geekmengran/MQ/2.Images/MQ-F-v1p5.png

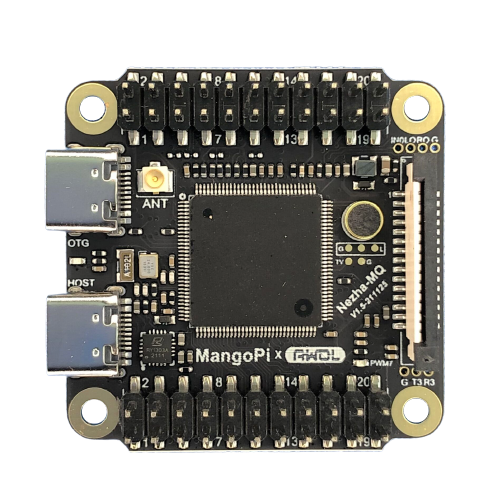
2.Images/MQ-F-v1p5.png
