geekmengran/MQ/3.Docs/MQ_SCH_v1.5.pdf

# J3USB-TypeC-16P

5.1K R80

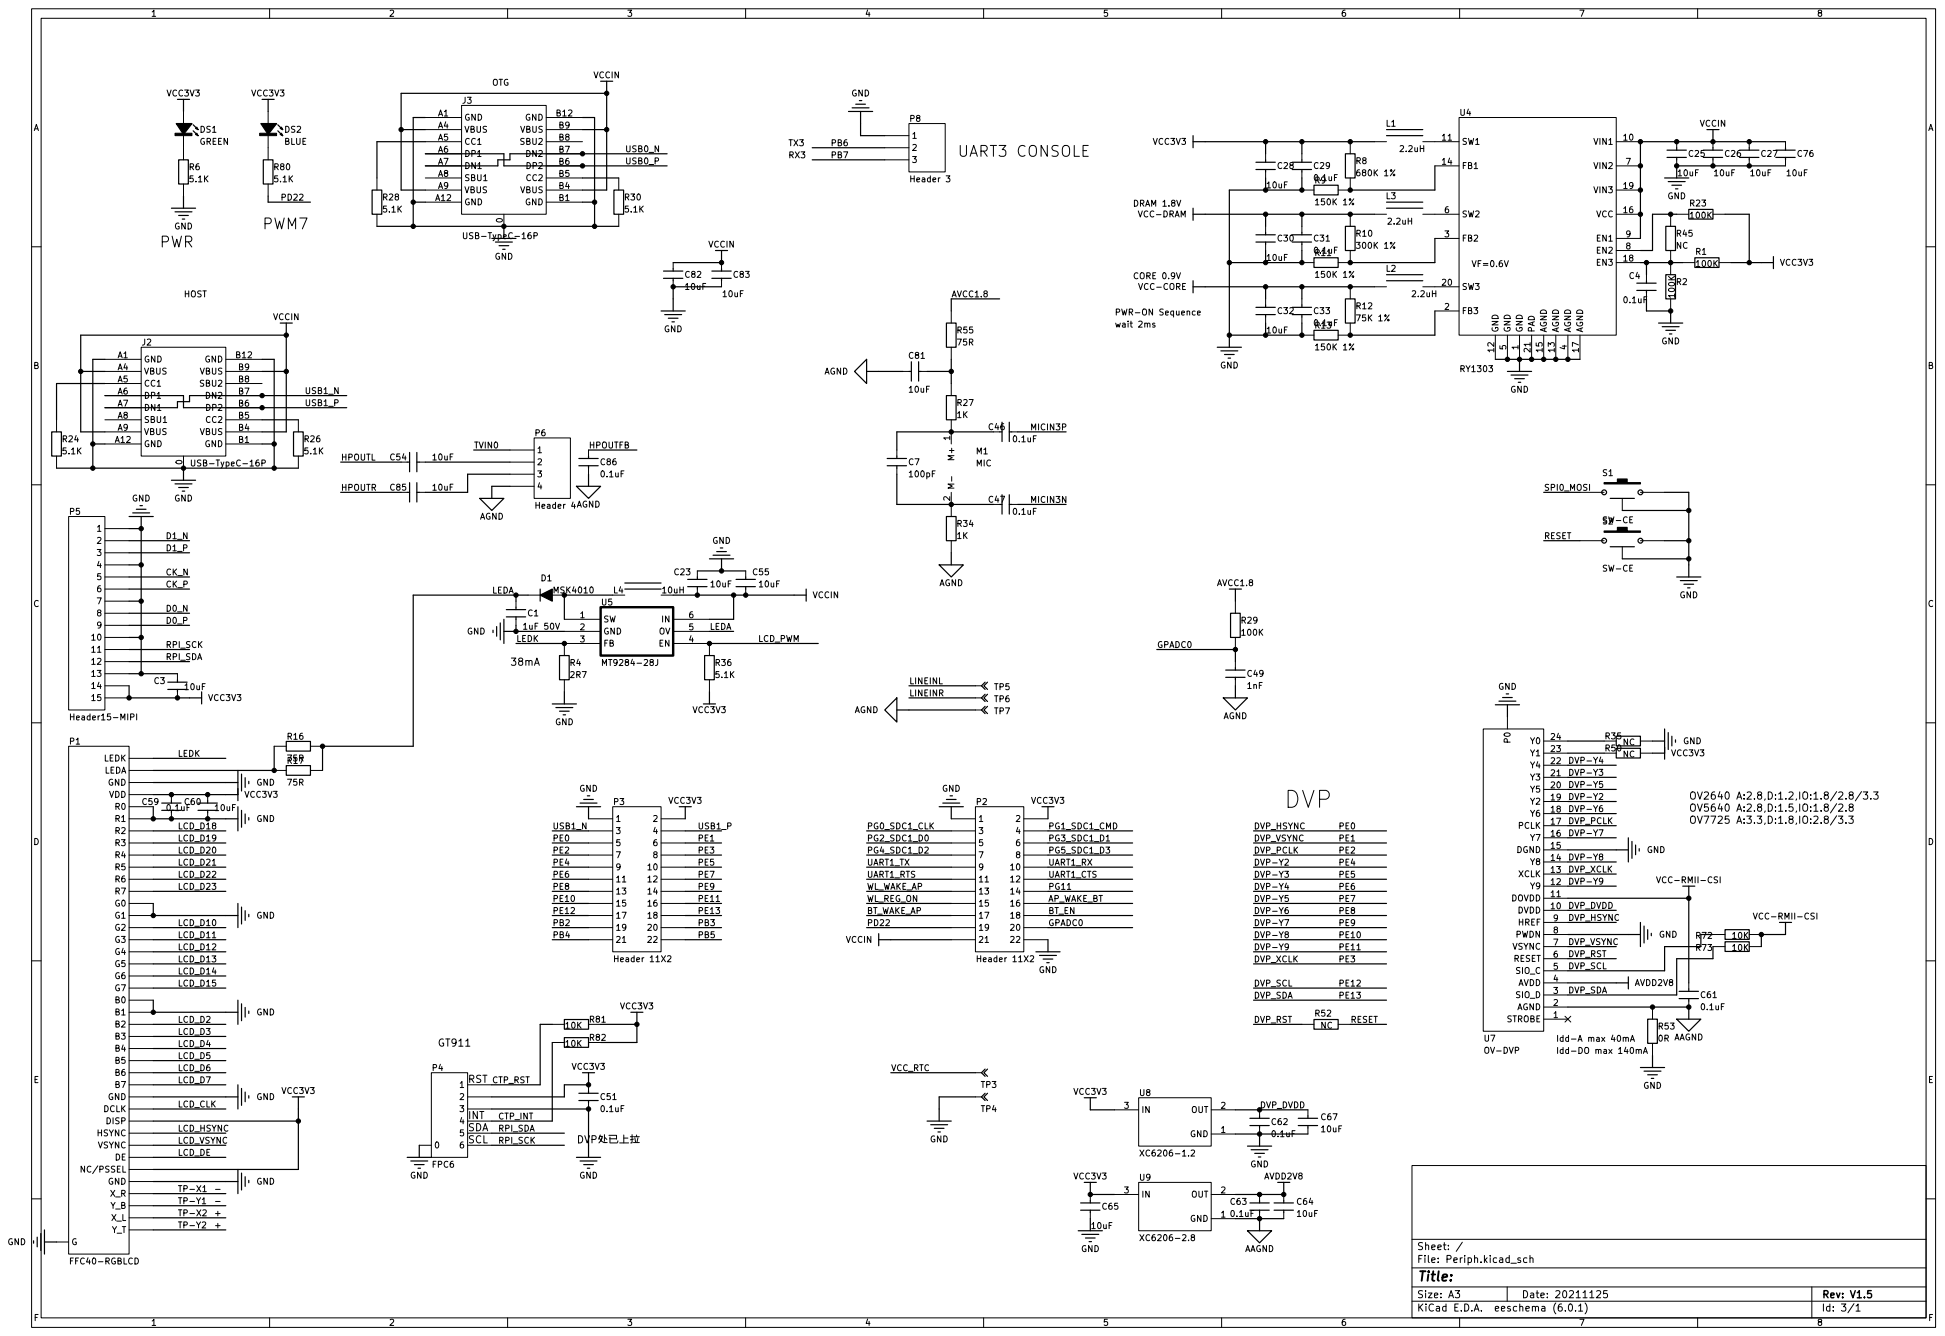
[picture p32: page 1]

0 GND A1 GND A12 VBUS A4 CC1 A5 DP1 A6 DN1 A7 SBU1 A8 VBUS A9 GND B1 GND B12 VBUS B4 CC2 B5 DP2 B6 DN2 B7 SBU2 B8 VBUS B9

1 VIN1 10 SW1 11 GND 12 AGND 13 FB1 14 AGND 15 VCC 16 AGND 17 EN3 18 VIN3 19 FB3 2 SW3 20 PAD 21 FB2 3 AGND

VSYNC
DE NC/PSSEL GND

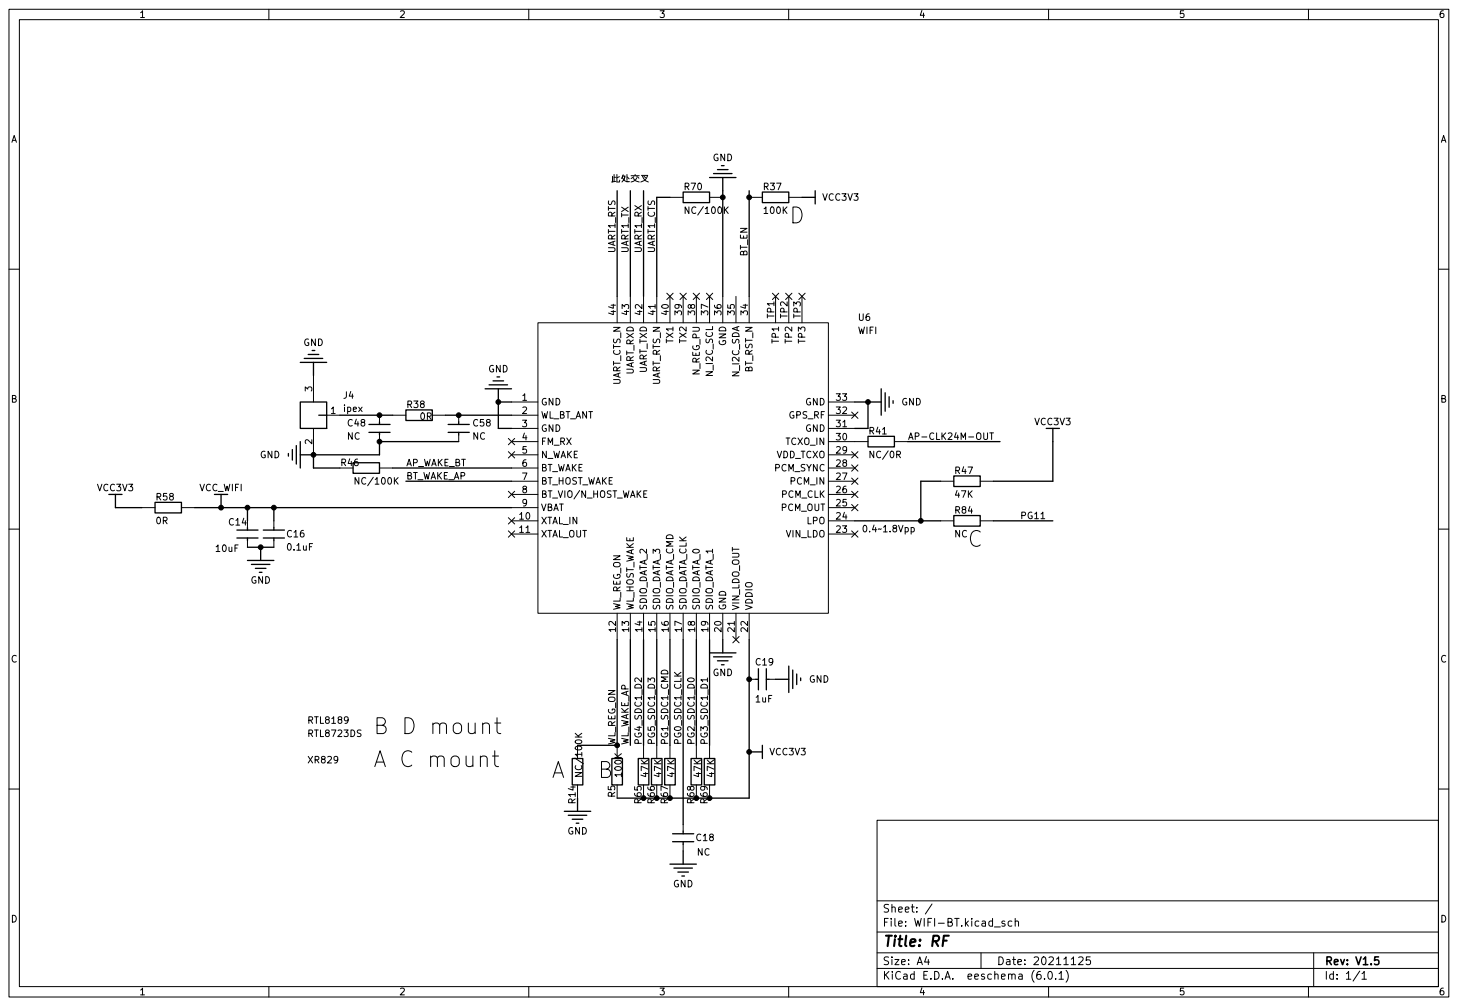
[picture p33: page 2]

File: WIFI-BT.kicad_sch Sheet: / VCC3V3 GND

# 0.1uF R59

# 0.1uF R71

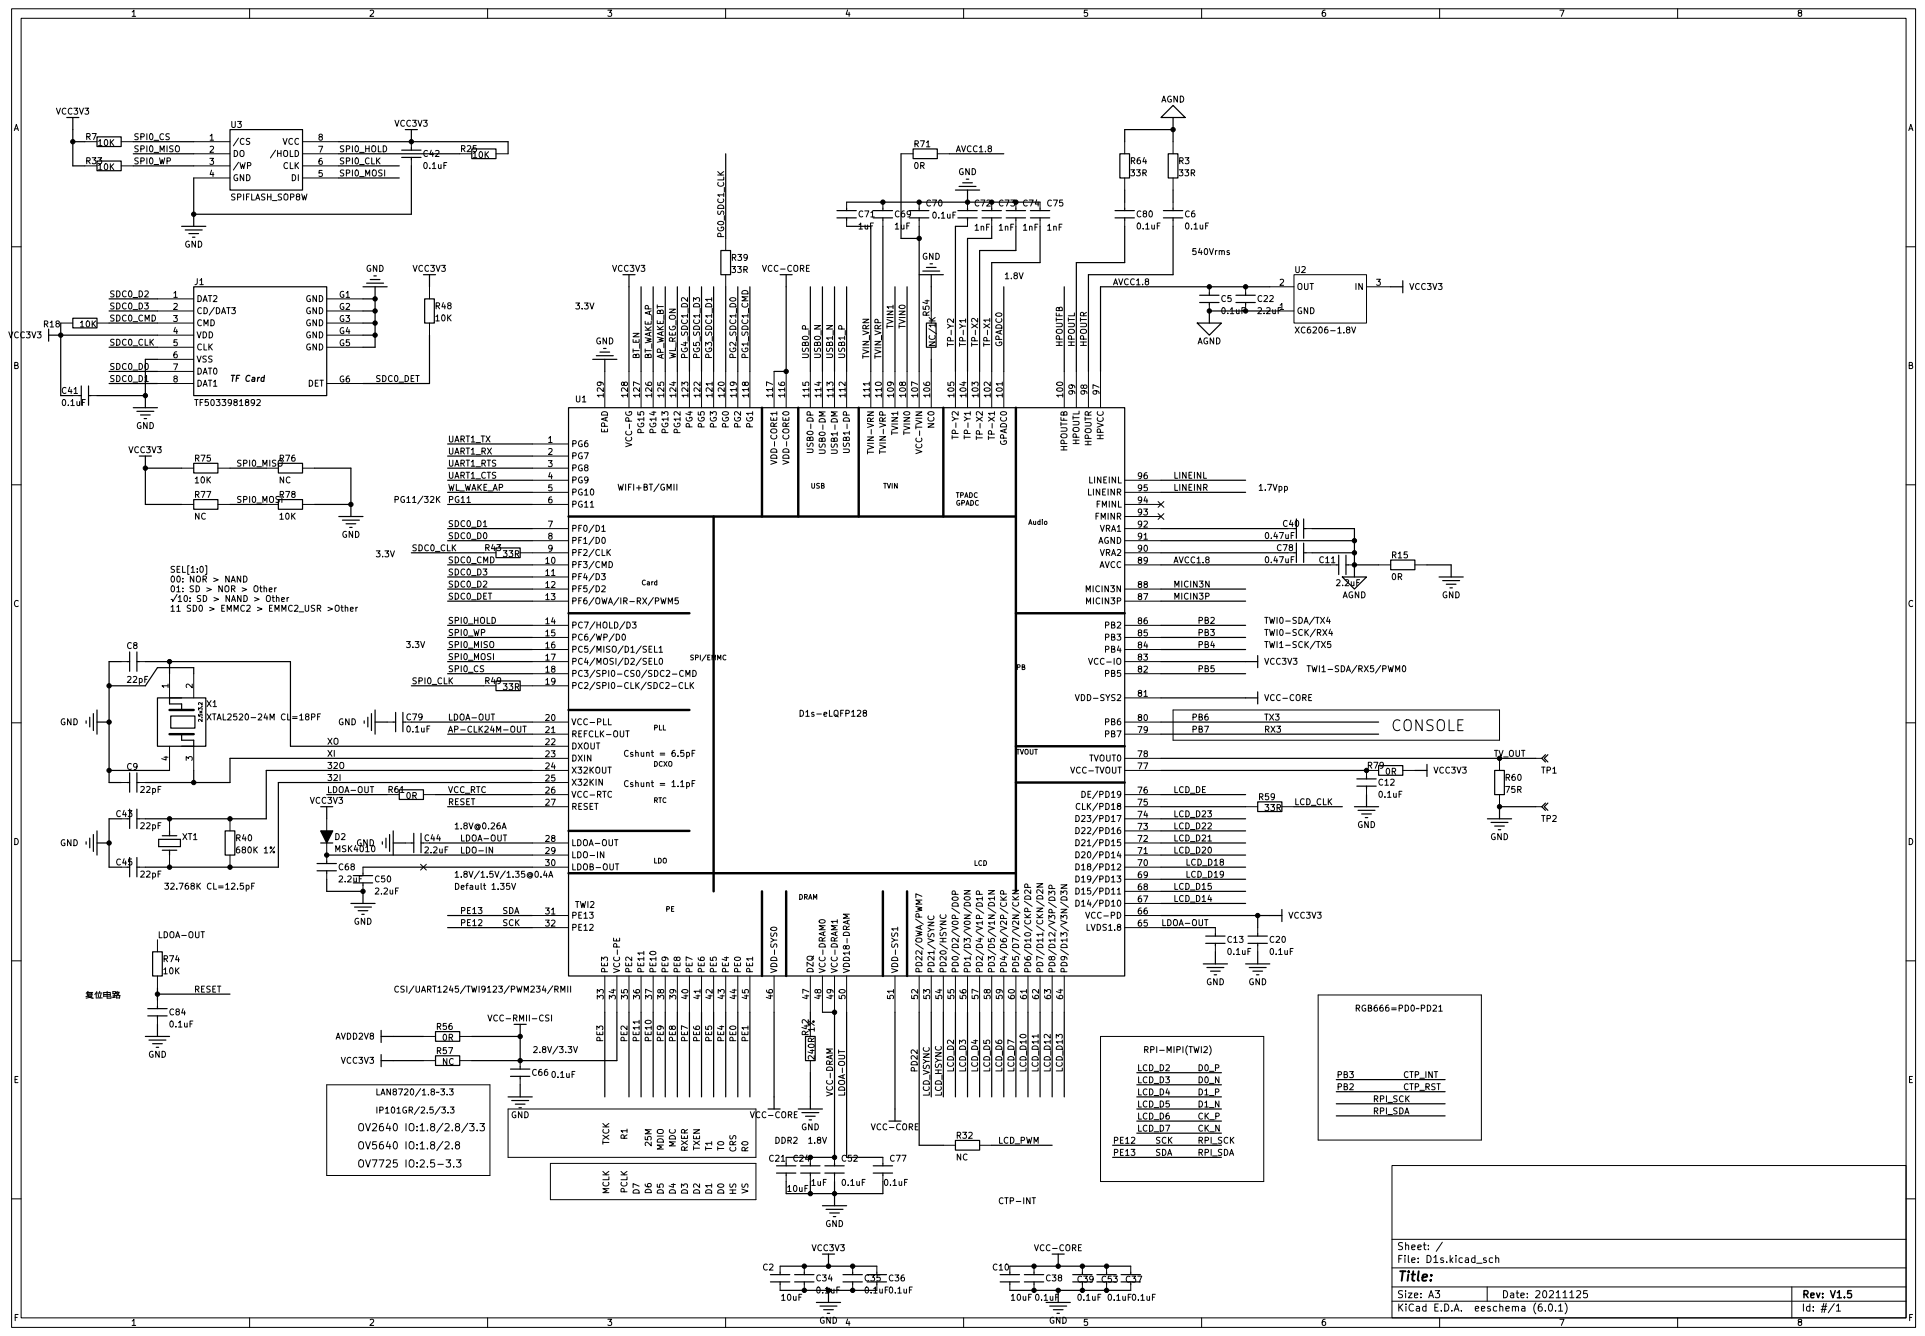
[picture p34: page 3]

01: SD > NOR > Other þÿ"10: SD > NAND > Other 11 SD0 > EMMC2 > EMMC2_USR >Other
